Cobertos/CSGO-StatTrak-Nerf-Arduino-Mod/displayDotsMod62.c

/*
  Fontname: DisplayDotsMod62
  Based off of DustBust (Andreas Nylin) - Display Dots
  https://www.dafont.com/display-dots.font
  
  Capital A Height: 38, '1' Height: 54
  Calculated Max Values w=38 h=54 x= 3 y=24 dx=44 dy= 0 ascent=54 len=216
  Font Bounding box     w=60 h=61 x= 0 y=-8
  Calculated Min Values           x= 0 y=-8 dx= 0 dy= 0
  Pure Font   ascent =38 descent= 0
  X Font      ascent =54 descent= 0
  Max Font    ascent =54 descent=-8
*/
#include "clib/u8g.h"
const u8g_fntpgm_uint8_t displayDotsMod62[8341] U8G_FONT_SECTION("displayDotsMod62") = {
  0,60,61,0,248,38,15,251,0,0,32,87,0,54,248,54,
  0,0,0,0,28,0,0,6,54,54,12,3,0,120,252,252,
  252,252,120,0,0,120,252,252,252,252,120,0,0,120,252,252,
  252,252,120,0,0,120,252,252,252,252,120,0,0,120,252,252,
  252,252,120,0,0,0,0,0,0,0,0,0,0,120,252,252,
  252,252,120,14,14,28,20,3,24,120,120,252,252,252,252,252,
  252,252,252,120,120,0,0,0,0,120,120,252,252,252,252,252,
  252,252,252,120,120,38,38,190,44,3,0,0,120,0,120,0,
  0,252,0,252,0,0,252,0,252,0,0,252,0,252,0,0,
  252,0,252,0,0,120,0,120,0,0,0,0,0,0,0,0,
  0,0,0,120,120,120,120,120,252,252,252,252,252,252,252,252,
  252,252,252,252,252,252,252,252,252,252,252,252,120,120,120,120,
  120,0,0,0,0,0,0,0,0,0,0,0,120,0,120,0,
  0,252,0,252,0,0,252,0,252,0,0,252,0,252,0,0,
  252,0,252,0,0,120,0,120,0,0,0,0,0,0,0,0,
  0,0,0,120,120,120,120,120,252,252,252,252,252,252,252,252,
  252,252,252,252,252,252,252,252,252,252,252,252,120,120,120,120,
  120,0,0,0,0,0,0,0,0,0,0,0,120,0,120,0,
  0,252,0,252,0,0,252,0,252,0,0,252,0,252,0,0,
  252,0,252,0,0,120,0,120,0,30,54,216,36,3,248,0,
  0,120,0,0,0,252,0,0,0,252,0,0,0,252,0,0,
  0,252,0,0,0,120,0,0,0,0,0,0,0,0,0,0,
  120,120,120,0,252,252,252,0,252,252,252,0,252,252,252,0,
  252,252,252,0,120,120,120,0,0,0,0,0,0,0,0,120,
  0,0,0,252,0,0,0,252,0,0,0,252,0,0,0,252,
  0,0,0,120,0,0,0,0,0,0,0,0,0,0,0,0,
  120,120,0,0,252,252,0,0,252,252,0,0,252,252,0,0,
  252,252,0,0,120,120,0,0,0,0,0,0,0,0,0,0,
  0,0,120,0,0,0,252,0,0,0,252,0,0,0,252,0,
  0,0,252,0,0,0,120,0,0,0,0,0,0,0,0,120,
  120,120,0,252,252,252,0,252,252,252,0,252,252,252,0,252,
  252,252,0,120,120,120,0,0,0,0,0,0,0,0,0,0,
  120,0,0,0,252,0,0,0,252,0,0,0,252,0,0,0,
  252,0,0,0,120,0,0,38,38,190,44,3,0,120,0,0,
  0,120,252,0,0,0,252,252,0,0,0,252,252,0,0,0,
  252,252,0,0,0,252,120,0,0,0,120,0,0,0,0,0,
  0,0,0,0,0,0,0,0,120,0,0,0,0,252,0,0,
  0,0,252,0,0,0,0,252,0,0,0,0,252,0,0,0,
  0,120,0,0,0,0,0,0,0,0,0,0,0,0,0,120,
  0,0,0,0,252,0,0,0,0,252,0,0,0,0,252,0,
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
